freeDSP/FreeDSP_INTEGRA/KiCAD_Files/FreeDSP_INTEGRA_PANELBOARD/Picture/FreeDSP_INTEGRA_PANEL_PCB_ParseUpfront.jpg

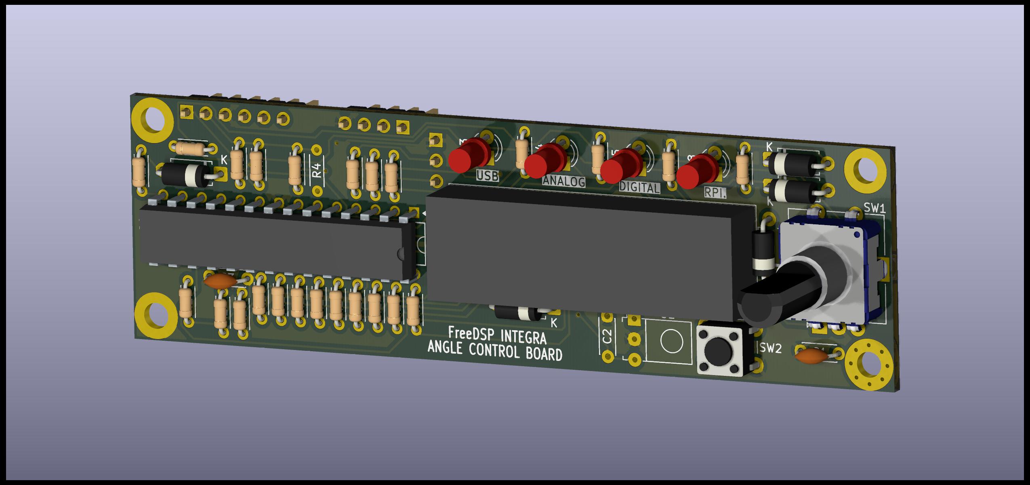
KiCAD_Files/FreeDSP_INTEGRA_PANELBOARD/Picture/FreeDSP_INTEGRA_PANEL_PCB_ParseUpfront.jpg
