freeDSP/FreeDSP_INTEGRA/KiCAD_Files/FreeDSP_INTEGRA_QUAD-PRO/Picture/FreeDSP_INTEGRA_QUAD-PRO_BotomView.jpg

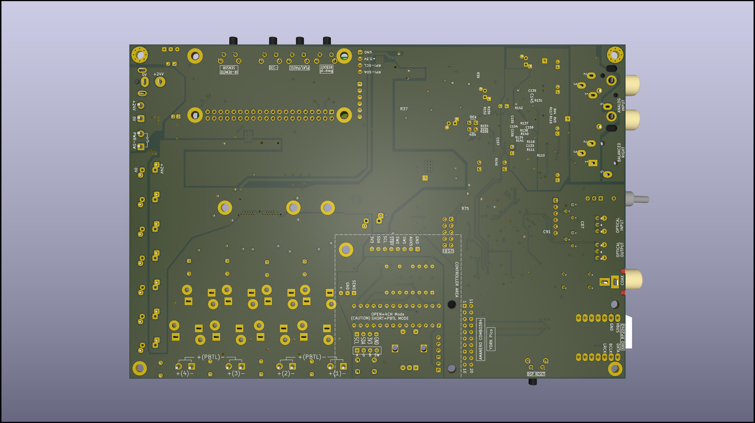
KiCAD_Files/FreeDSP_INTEGRA_QUAD-PRO/Picture/FreeDSP_INTEGRA_QUAD-PRO_BotomView.jpg
