freeDSP/FreeDSP_INTEGRA/KiCAD_Files/FreeDSP_INTEGRA_QUAD-PRO/JLCPCB_OrderFiles/Top+null+SMT026041161394.png

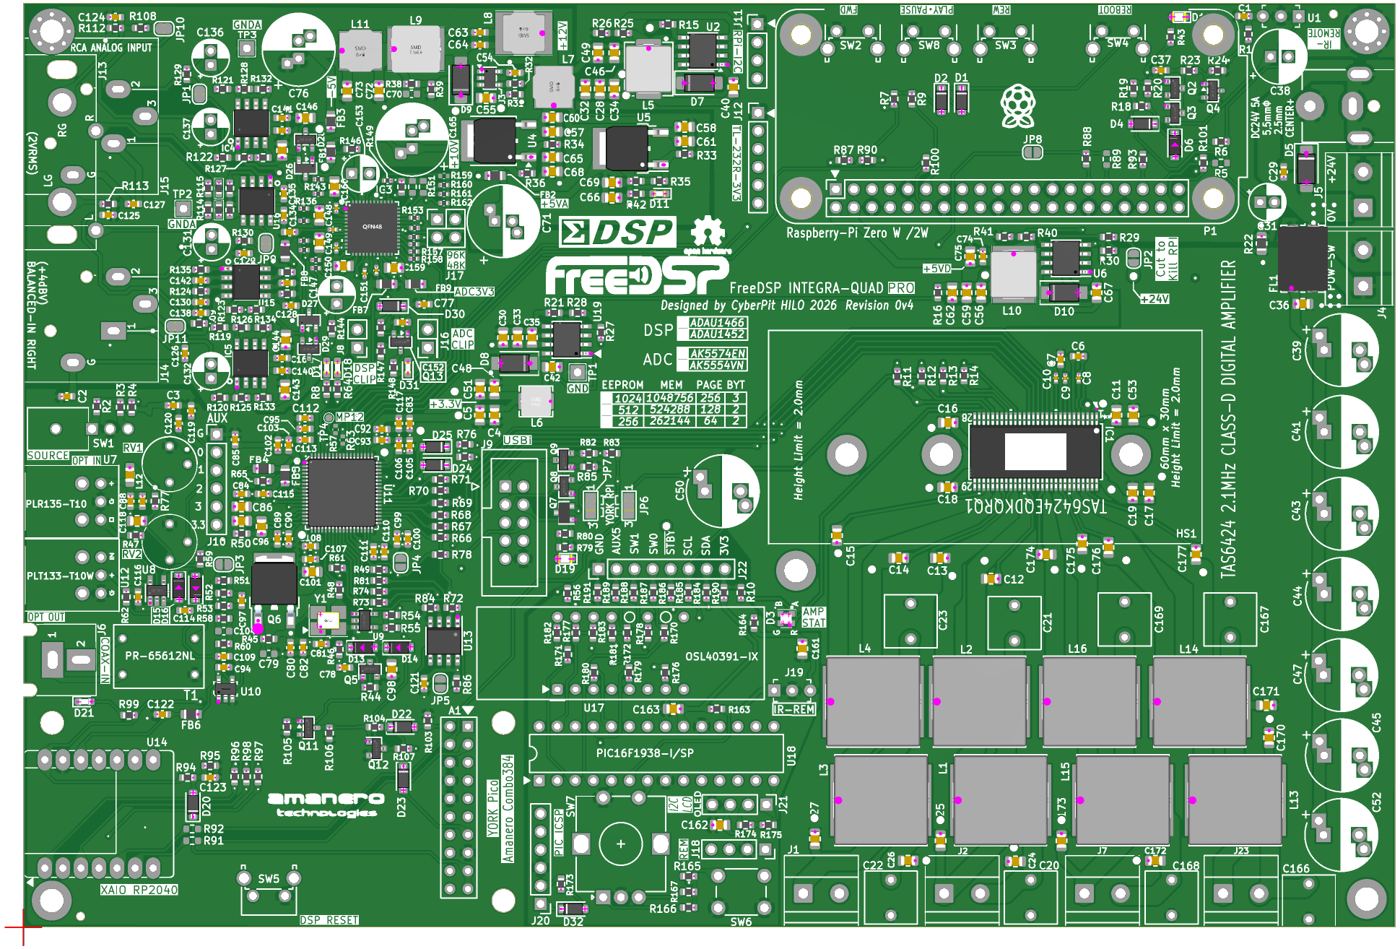
KiCAD_Files/FreeDSP_INTEGRA_QUAD-PRO/JLCPCB_OrderFiles/Top+null+SMT026041161394.png
